RaviKachhwaha/AuraForge-50X/docs/images/drc_zero_errors.png

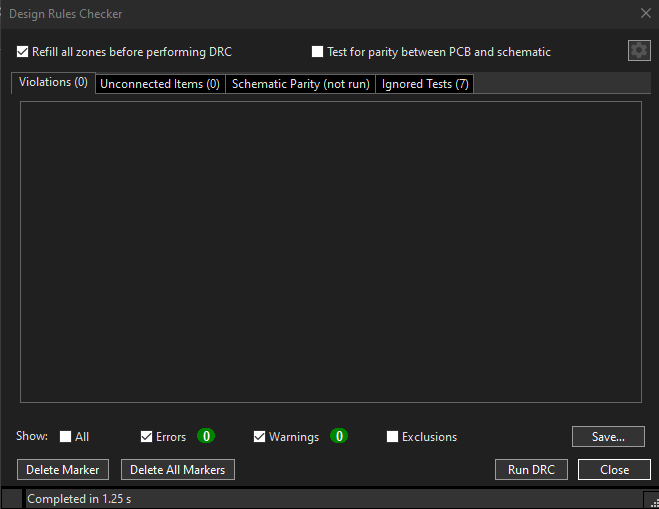
docs/images/drc_zero_errors.png
