RaviKachhwaha/AuraForge-50X/docs/images/UI main page first view 1.png

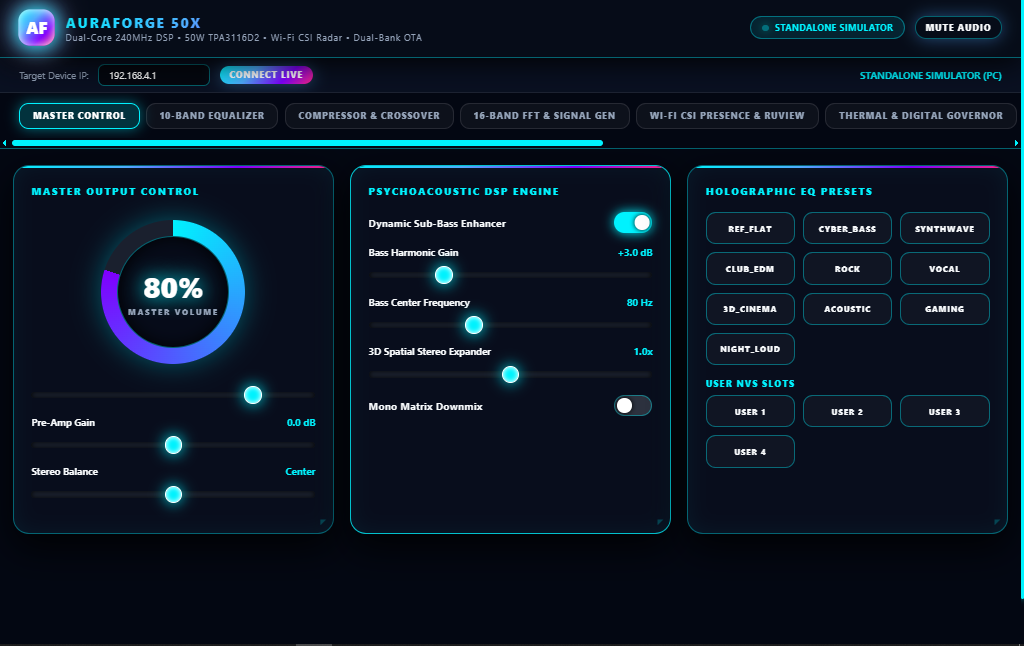
docs/images/UI main page first view 1.png
