RaviKachhwaha/AuraForge-50X/docs/images/UI main page first view 5.png

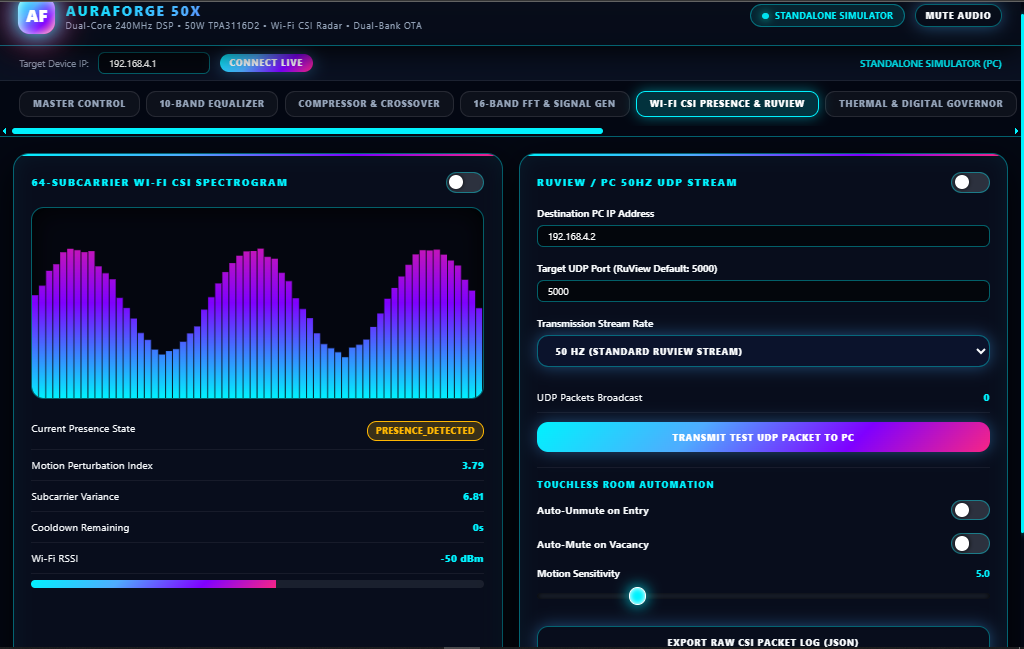
docs/images/UI main page first view 5.png
