RaviKachhwaha/AuraForge-50X/docs/images/UI main page first view 6.png

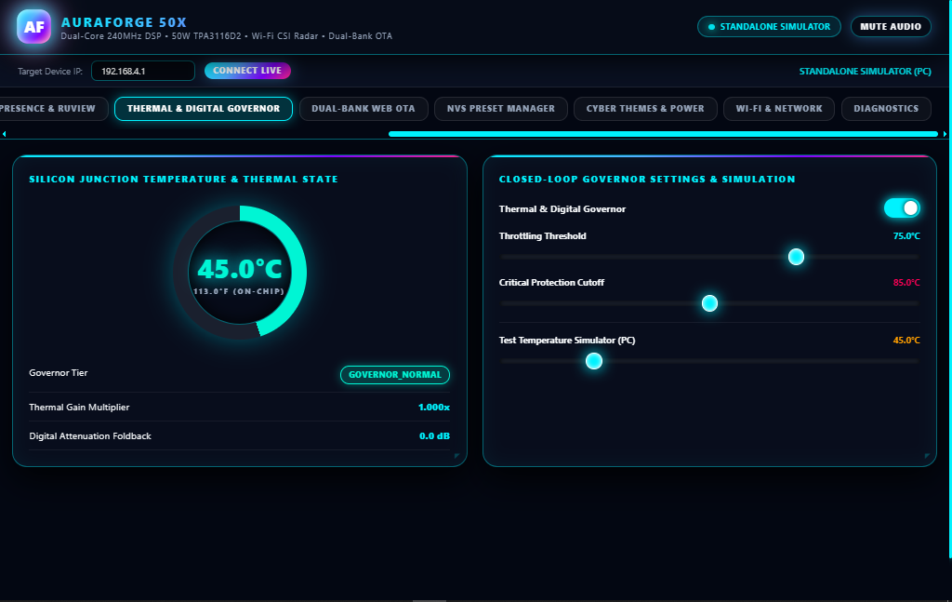
docs/images/UI main page first view 6.png
